MaximumP/Haminet/src/config.py

import ujson
import os


class Config:
    _target_temperature: float
    _temperature_tolerance: float
    _target_humidity: float
    _humidity_tolerance: float
    _config_file: str
    _fan_on_interval: int
    _fan_off_interval: int

    def __init__(self, config_file: str):
        self._config_file = config_file
        self._target_temperature = 6.0
        self._target_humidity = 70.0
        self._temperature_tolerance = 1.0
        self._humidity_tolerance = 2
        self._fan_on_interval = 2
        self._fan_off_interval = 60
        if config_file:
            if config_file in os.listdir():
                self._read_config_file()
            else:
                self._write_config_file()

    def get_target_temperature(self):
        return self._target_temperature

    def set_target_temperature(self, value: float):
        if self._target_temperature != value:
            self._target_temperature = value
            self._write_config_file()

    def get_target_humidity(self):
        return self._target_humidity

    def set_target_humidity(self, value: float):
        if self._target_humidity != value:
            self._target_humidity = value
            self._write_config_file()

    def get_temperature_tolerance(self):
        return self._temperature_tolerance

    def set_temperature_tolerance(self, value: float):
        if self._temperature_tolerance != value:
            self._temperature_tolerance = value
            self._write_config_file()

    def get_humidity_tolerance(self):
        return self._humidity_tolerance

    def set_humidity_tolerance(self, value: float):
        if self._humidity_tolerance != value:
            self._humidity_tolerance = value
            self._write_config_file()

    def get_fan_on_interval(self):
        return self._fan_on_interval

    def set_fan_on_interval(self, value: int):
        if self._fan_on_interval != value:
            self._fan_on_interval = value
            self._write_config_file()

    def get_fan_off_interval(self):
        return self._fan_off_interval

    def set_fan_off_interval(self, value: int):
        if self._fan_off_interval != value:
            self._fan_off_interval = value
            self._write_config_file()

    def _read_config_file(self):
        with open(self._config_file, "r") as config_file:
            config = ujson.loads(config_file.read())
        if config:
            self._target_temperature = config.get("target_temperature")
            self._target_humidity = config.get("target_humidity")
            self._humidity_tolerance = config.get("humidity_tolerance")
            self._temperature_tolerance = config.get("temperature_tolerance")
            self._fan_on_interval = config.get("fan_on_interval")
            self._fan_off_interval = config.get("fan_off_interval")
            print("read config file")

    def _write_config_file(self):
        if self._config_file:
            json = ujson.dumps(
                {
                    "target_temperature": self._target_temperature,
                    "target_humidity": self._target_humidity,
                    "humidity_tolerance": self._humidity_tolerance,
                    "temperature_tolerance": self._temperature_tolerance,
                    "fan_on_interval": self._fan_on_interval,
                    "fan_off_interval": self._fan_off_interval,
                }
            )
            with open(self._config_file, "w") as config_file:
                config_file.write(json)
            print("created config file")
