MaximumP/Haminet/src/debounce.py

from machine import Timer
from micropython import schedule


def timer_init(timer, period, callback):
    timer.init(period=period, callback=callback)


class DebouncedSwitch:
    def __init__(self, sw, cb, arg=None, delay=50, tid=-1):
        self.sw = sw
        # Create references to bound methods beforehand
        # http://docs.micropython.org/en/latest/pyboard/library/micropython.html#micropython.schedule
        self._sw_cb = self.sw_cb
        self._tim_cb = self.tim_cb
        self._set_cb = getattr(self.sw, 'callback', None) or self.sw.irq
        self.delay = delay
        self.tim = Timer(tid)
        self.callback(cb, arg or sw)

    def sw_cb(self, pin=None):
        self._set_cb(None)
        timer_init(self.tim, self.delay, self._tim_cb)

    def tim_cb(self, tim):
        tim.deinit()
        if self.sw():
            schedule(self.cb, self.arg)
        self._set_cb(self._sw_cb if self.cb else None)

    def callback(self, cb, arg=None):
        self.tim.deinit()
        self.cb = cb
        self.arg = arg
        self._set_cb(self._sw_cb if cb else None)
